keawade/keaboard/images/keaboard.jpg

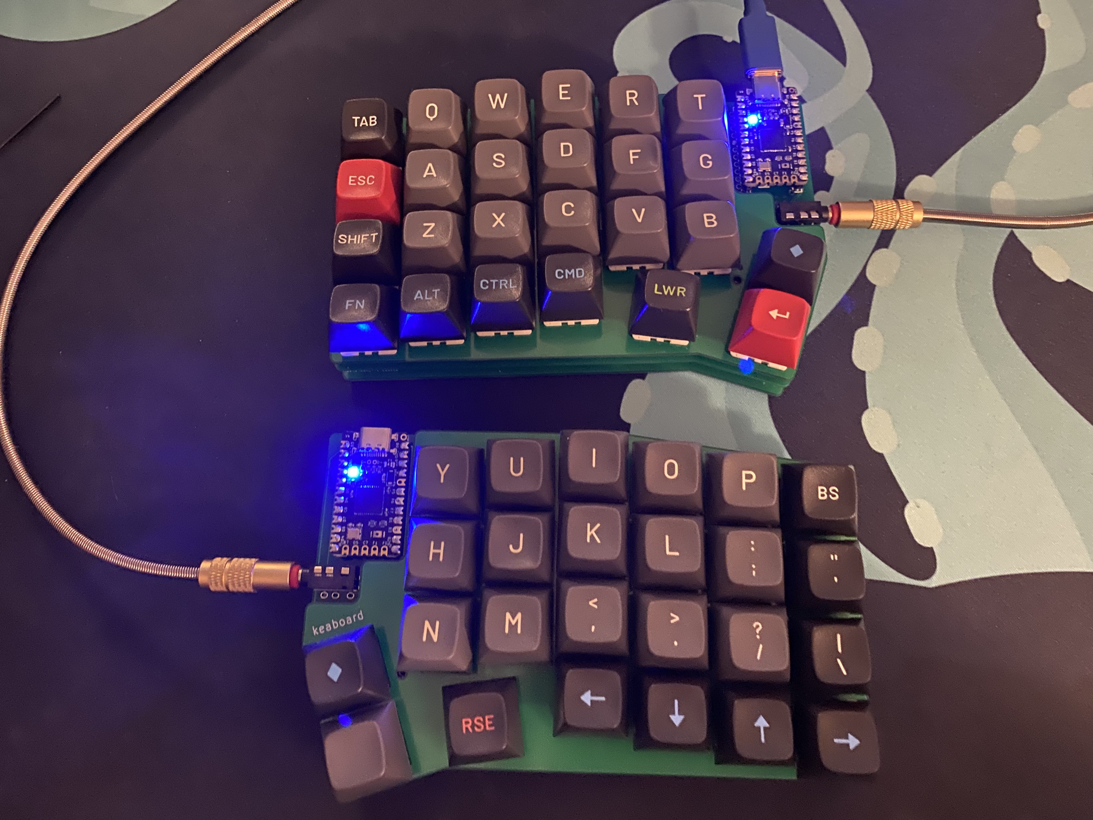
images/keaboard.jpg
