keawade/keaboard/PCB/keaboard_rev1/images/WIP_2020-08-22 15-57-15.png

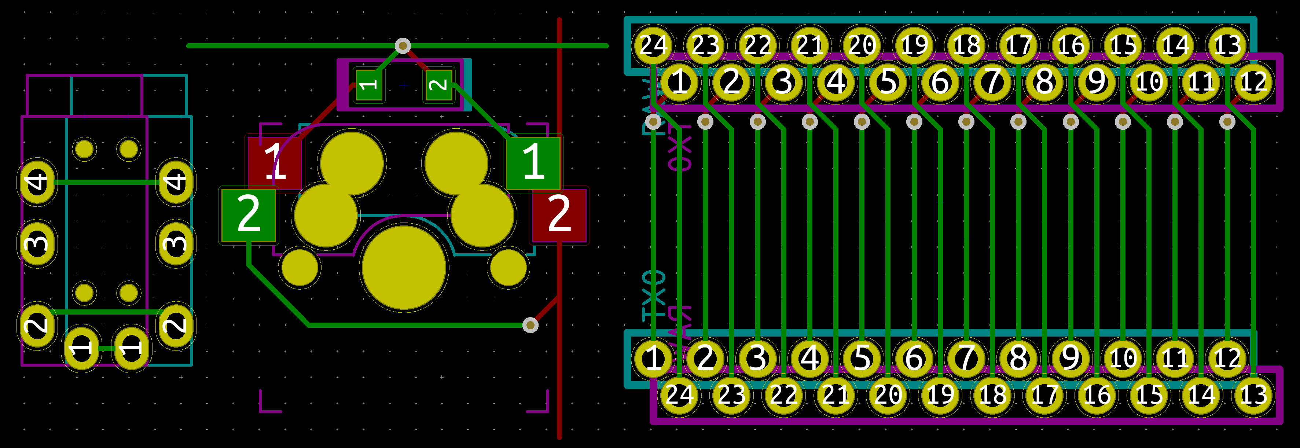
PCB/keaboard_rev1/images/WIP_2020-08-22 15-57-15.png
