keawade/keaboard/PCB/keaboard_rev1/images/WIP_2020-08-22 22-06-43.png

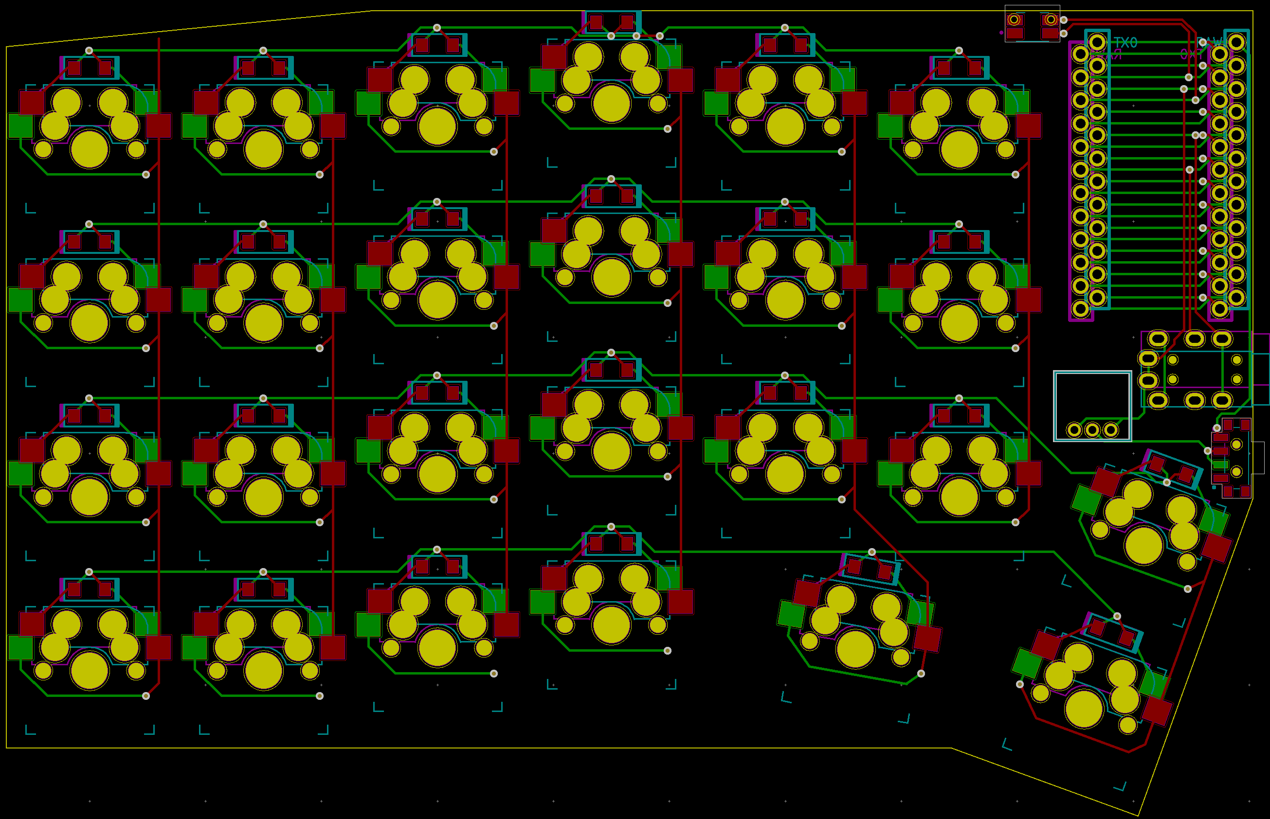
PCB/keaboard_rev1/images/WIP_2020-08-22 22-06-43.png
